matt-the-ogre/workbench/workbench-diagonal-perspective.png

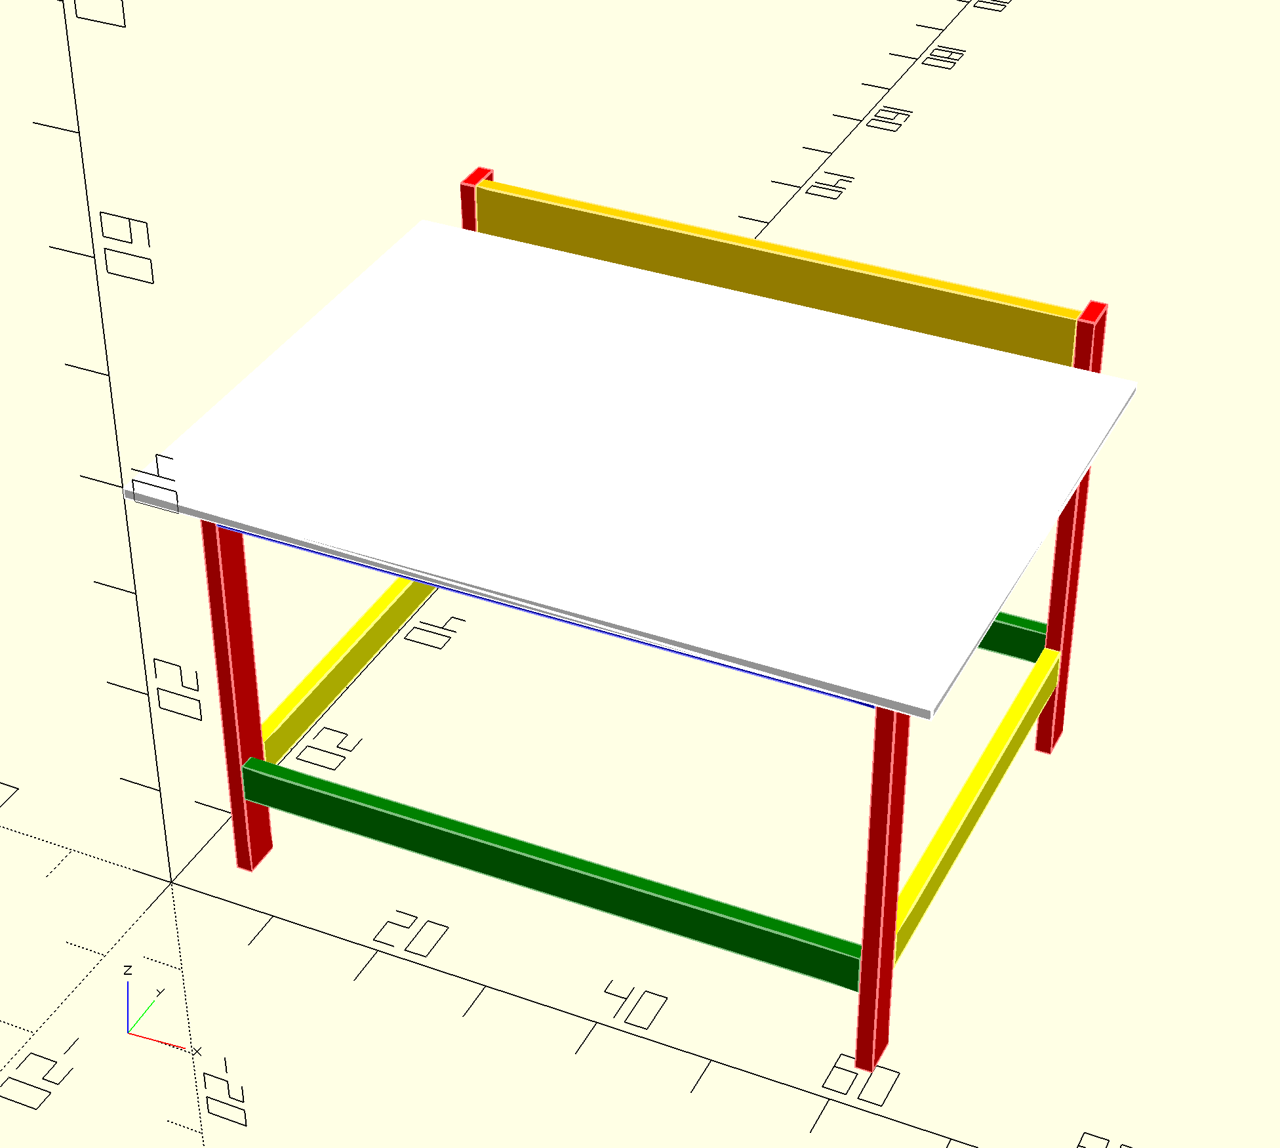
workbench-diagonal-perspective.png
